Runningtarrens/Mcorne/pics/20210213_094829.jpg

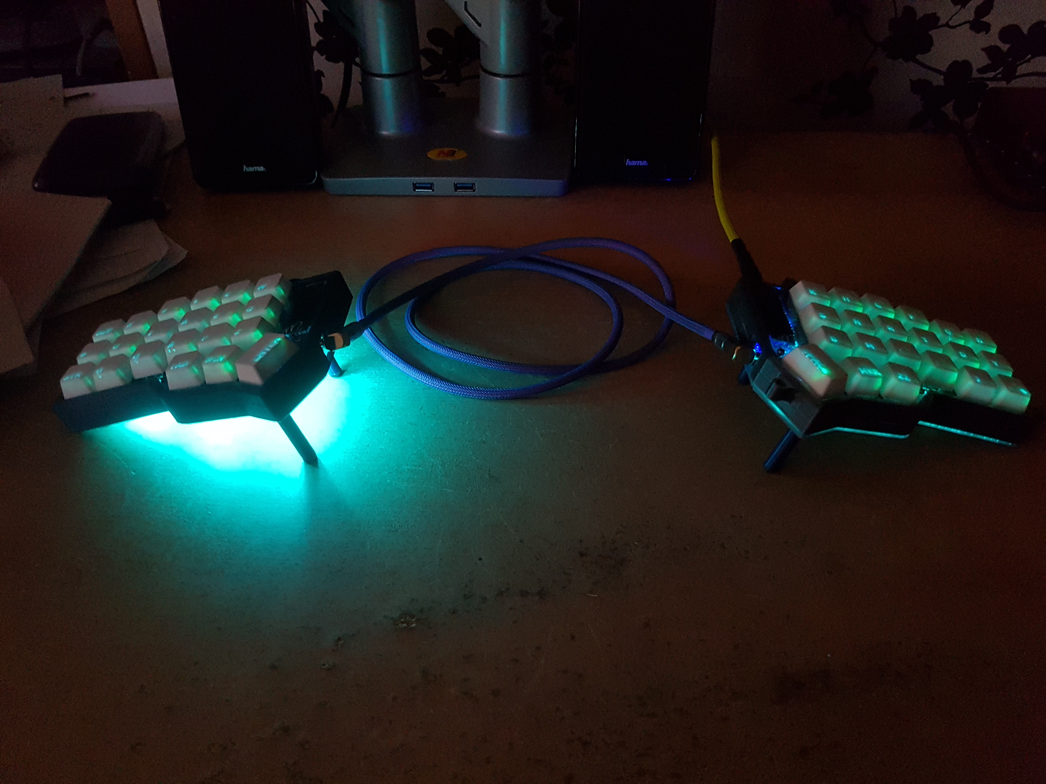
pics/20210213_094829.jpg
