Runningtarrens/Mcorne/pics/20210213_094833.jpg

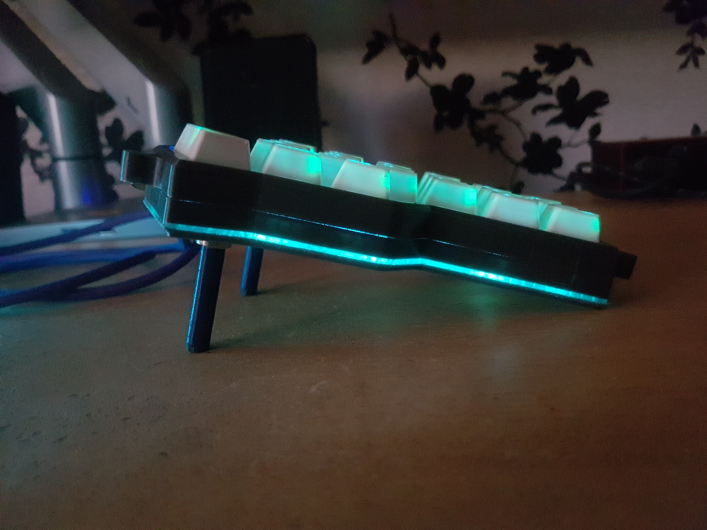
pics/20210213_094833.jpg
