Runningtarrens/Mcorne/pics/20210213_095013.jpg

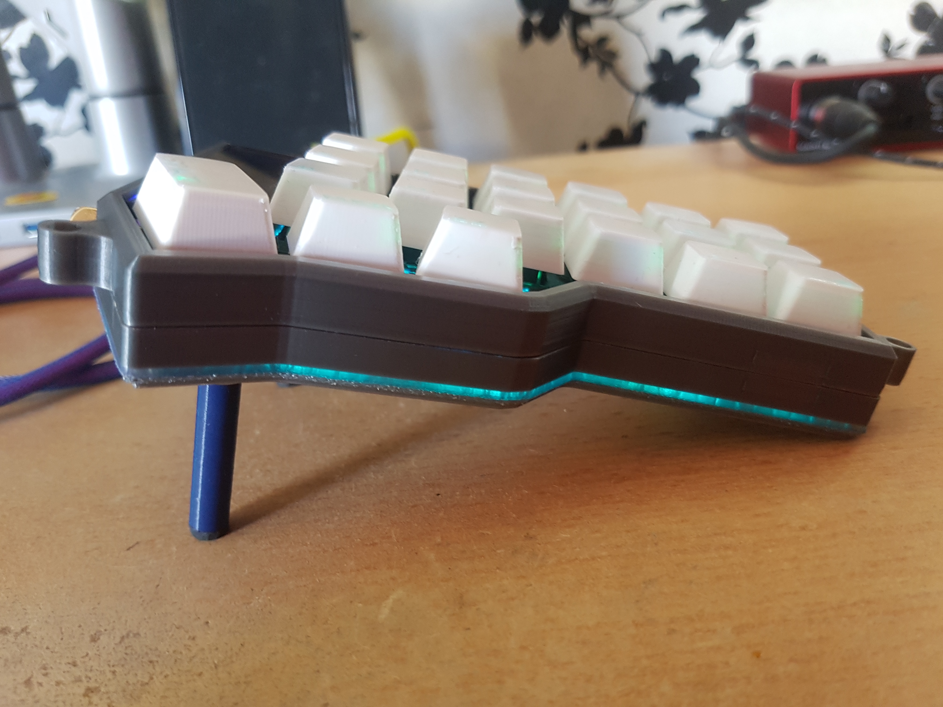
pics/20210213_095013.jpg
