Runningtarrens/Mcorne/pics/20210213_095016.jpg

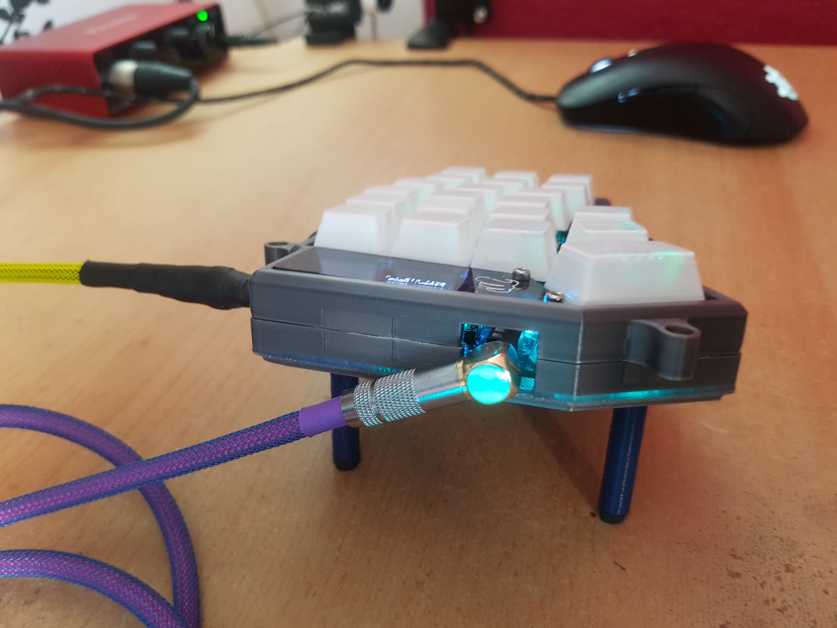
pics/20210213_095016.jpg
