Runningtarrens/Mcorne/pics/20210213_095025.jpg

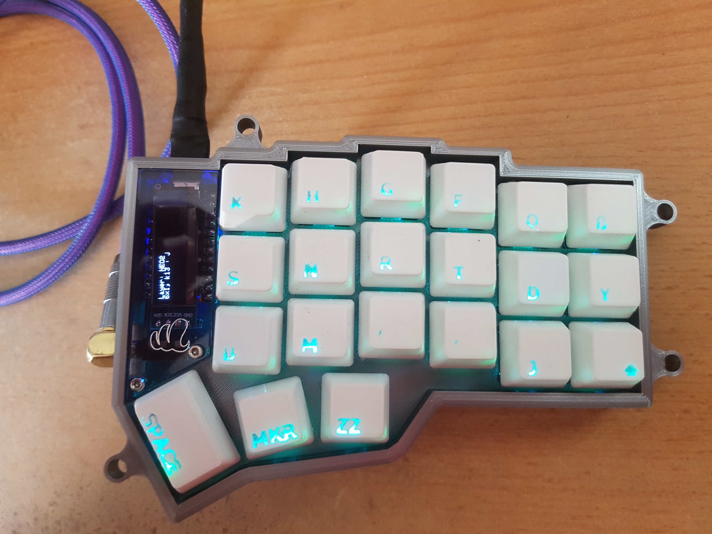
pics/20210213_095025.jpg
