Runningtarrens/Mcorne/pics/20210412_124343.jpg

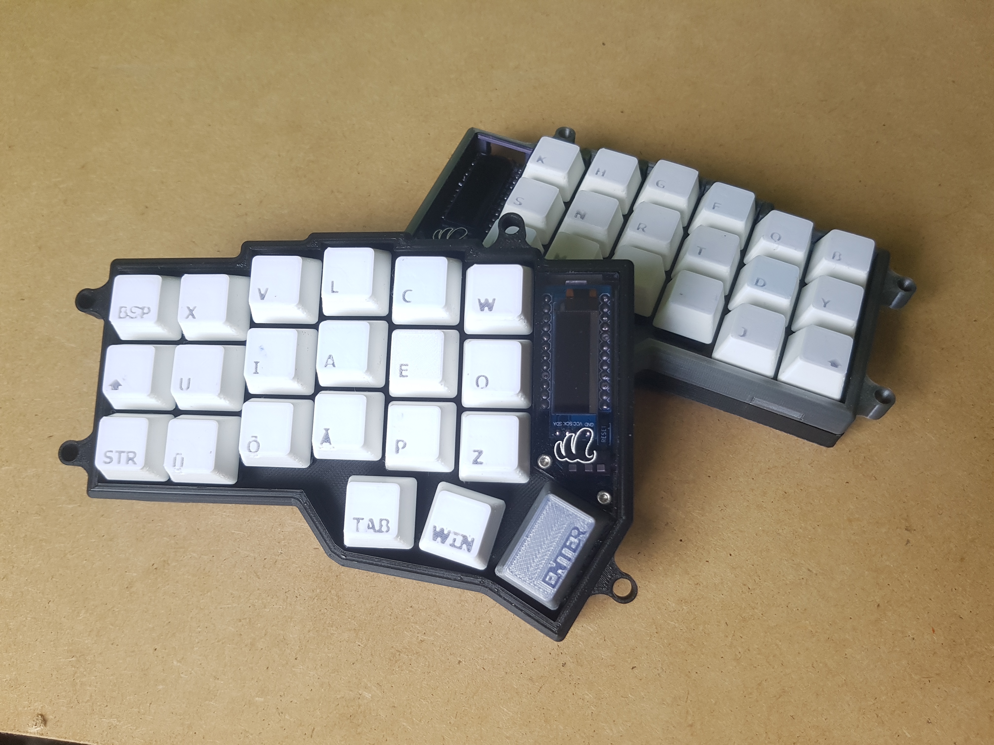
pics/20210412_124343.jpg
