Runningtarrens/Mcorne/pics/20210412_124447.jpg

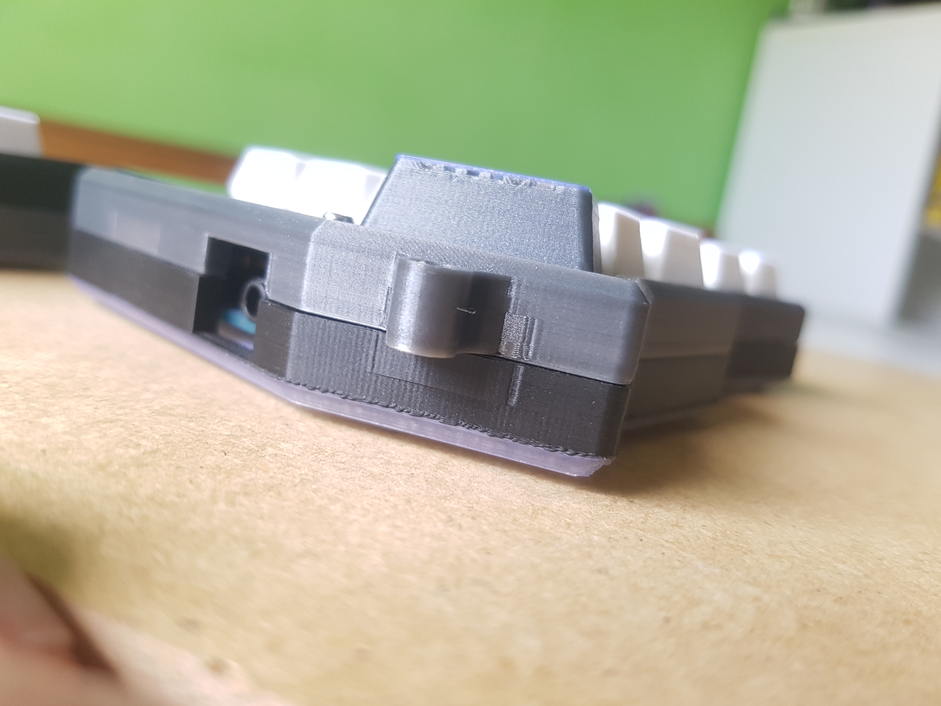
pics/20210412_124447.jpg
